telzo2000/cool950S/img/img0043.jpg

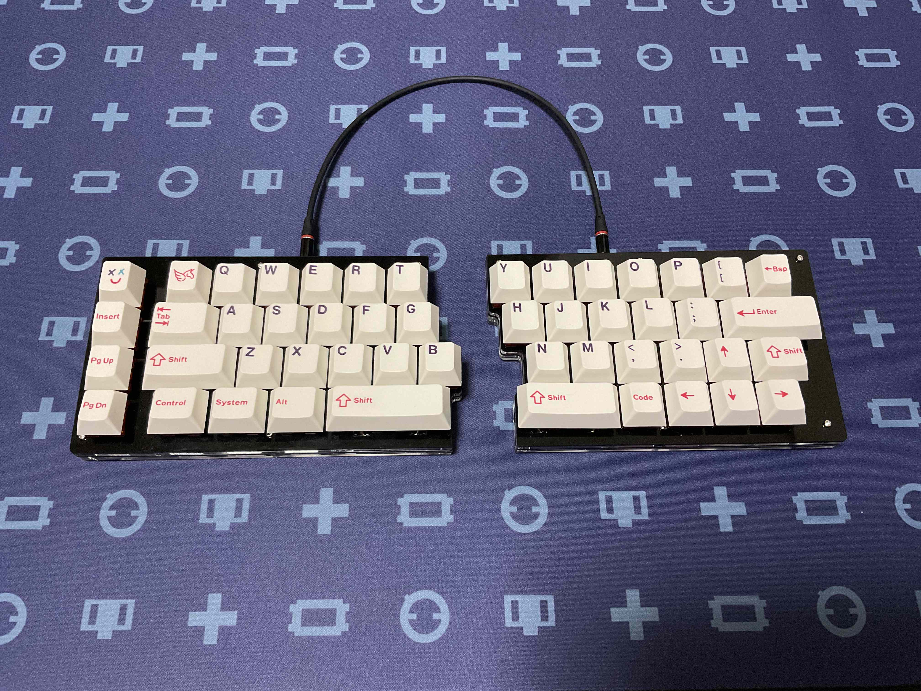
img/img0043.jpg
